atchesonUSC/sympl/source/pin_config.py

"""
This file contains pin mapping information for the Raspberry Pi 4
"""

# Reader -> Physical pin mapping
R0 = 26
R1 = 24
R2 = 1
R3 = 8
R4 = 36
R5 = 29
R6 = 31
R7 = 33
R8 = 35
R9 = 37
R10 = 11
R11 = 13
R12 = 15
R13 = 16
R14 = 18
R15 = 38

# Button -> Physical pin mapping
BUTTON = 40
